tudelft/event_orin_drone/pics/IMG_1040.jpg

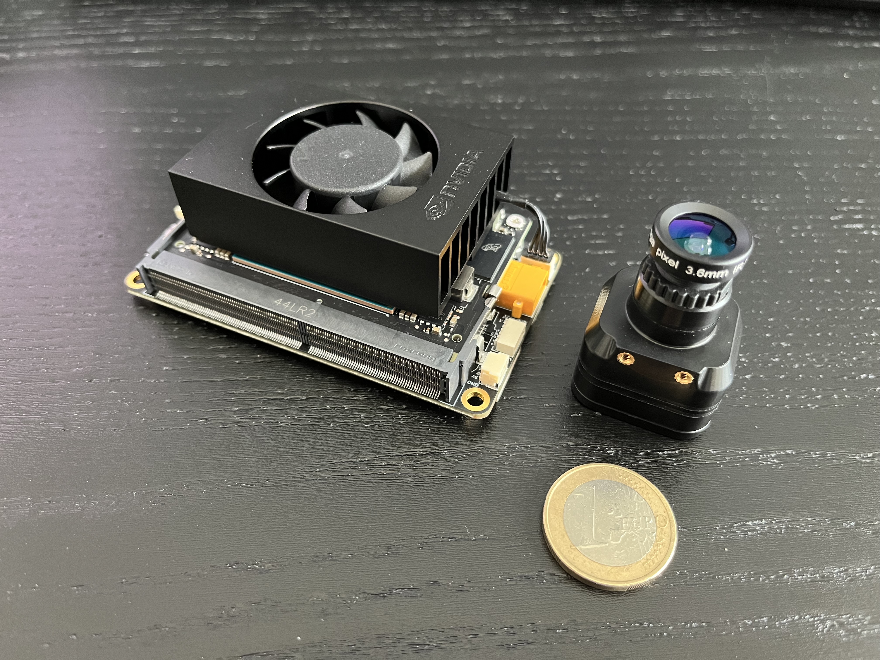
pics/IMG_1040.jpg
