tudelft/event_orin_drone/pics/IMG_1737.jpg

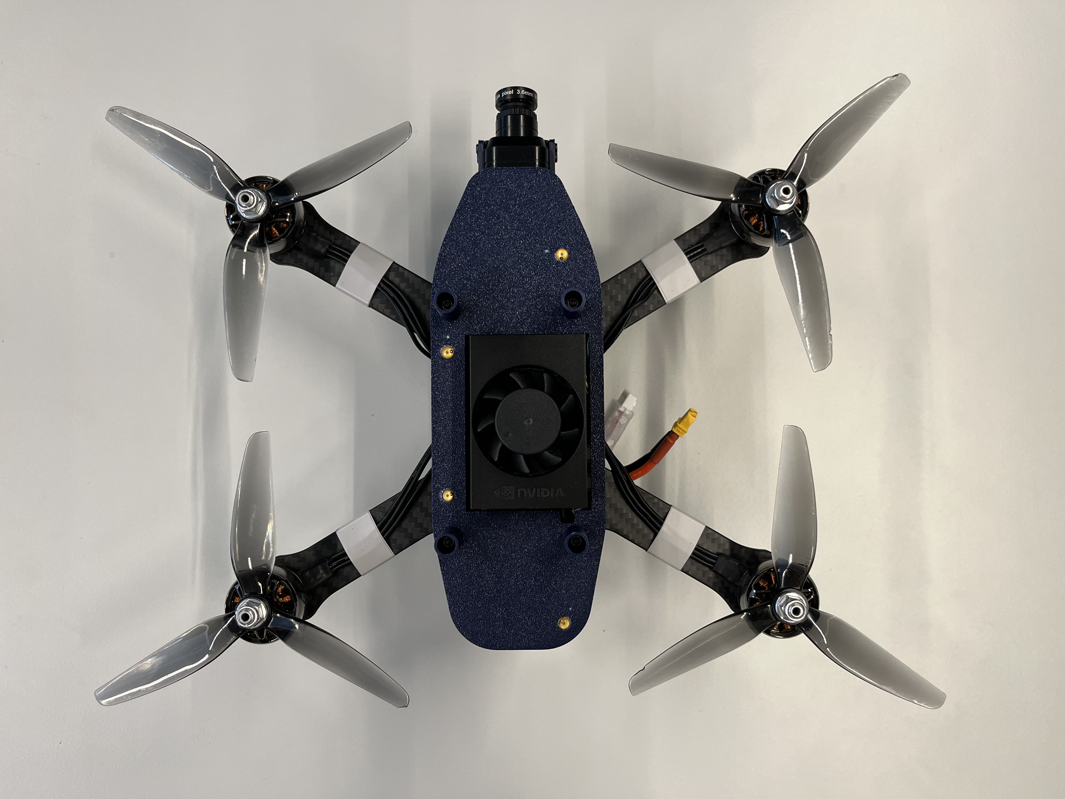
pics/IMG_1737.jpg
