tudelft/event_orin_drone/pics/IMG_1738.jpg

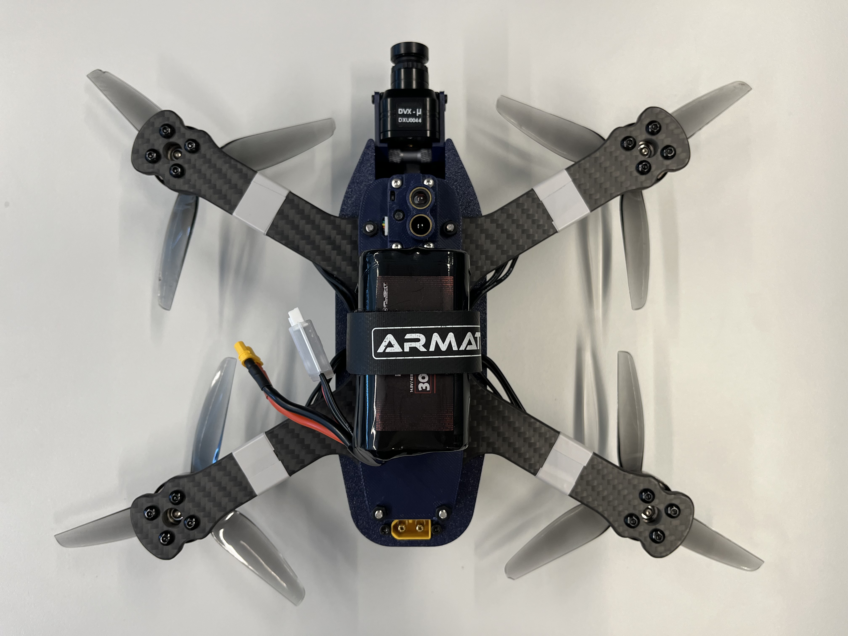
pics/IMG_1738.jpg
