tudelft/event_orin_drone/pics/IMG_2028.jpg

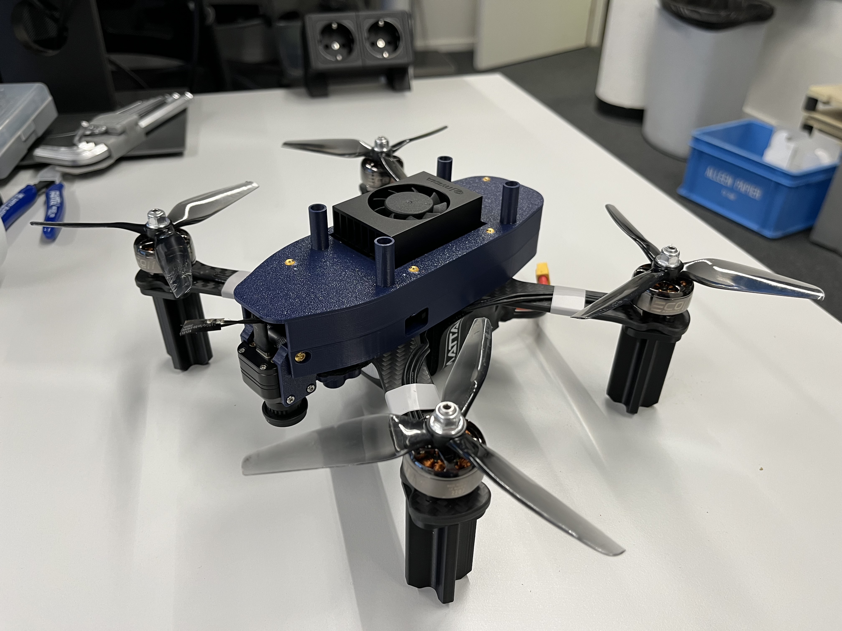
pics/IMG_2028.jpg
