tudelft/event_orin_drone/pics/IMG_2029.jpg

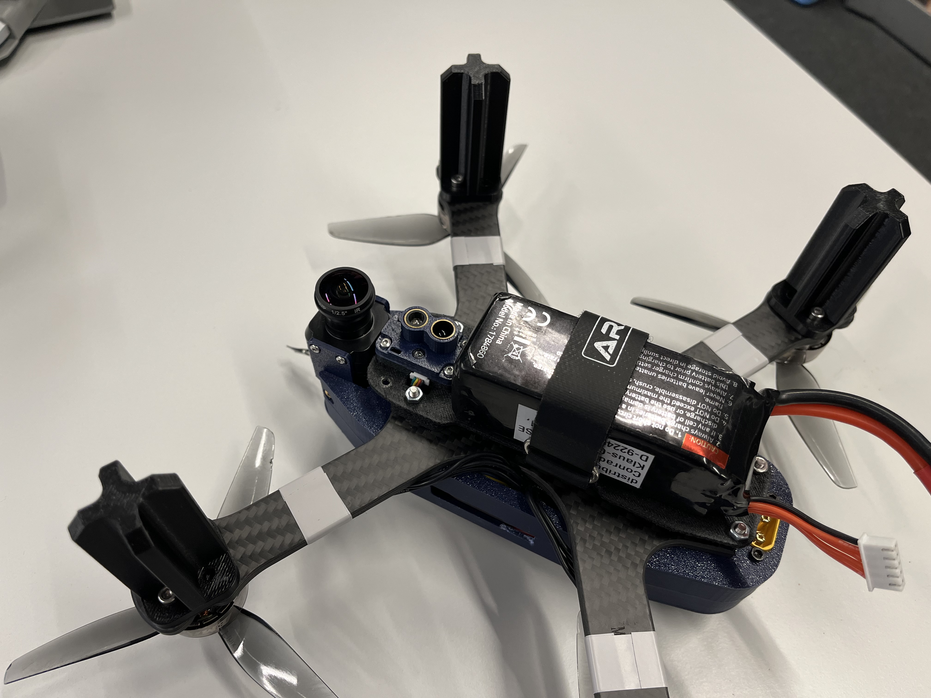
pics/IMG_2029.jpg
