tudelft/event_orin_drone/pics/IMG_1676.jpg

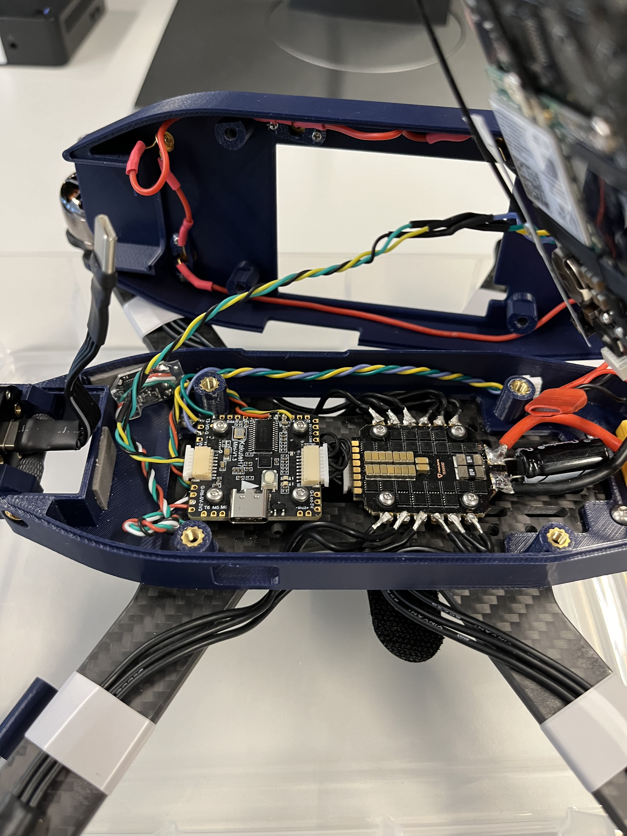
pics/IMG_1676.jpg
